josepala650/robofutbol/modelos 3d para imprimir/robot_futbool_02_rueda_loca_canica_mini.stl

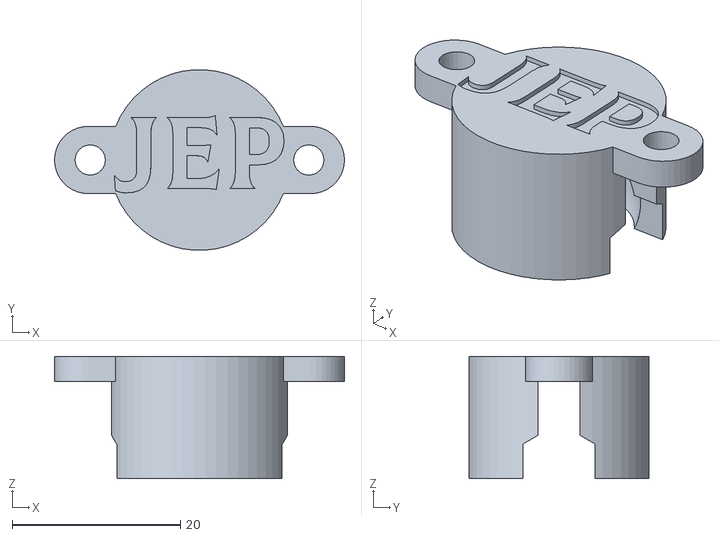
[picture p79: CAD file, 2022-09-19]
modelos 3d para imprimir/robot_futbool_02_rueda_loca_canica_mini.stl
34.5 x 21.5 x 14.6
