josepala650/robofutbol/modelos 3d para imprimir/robot_futbool_02_llanta_motor_arduino.stl

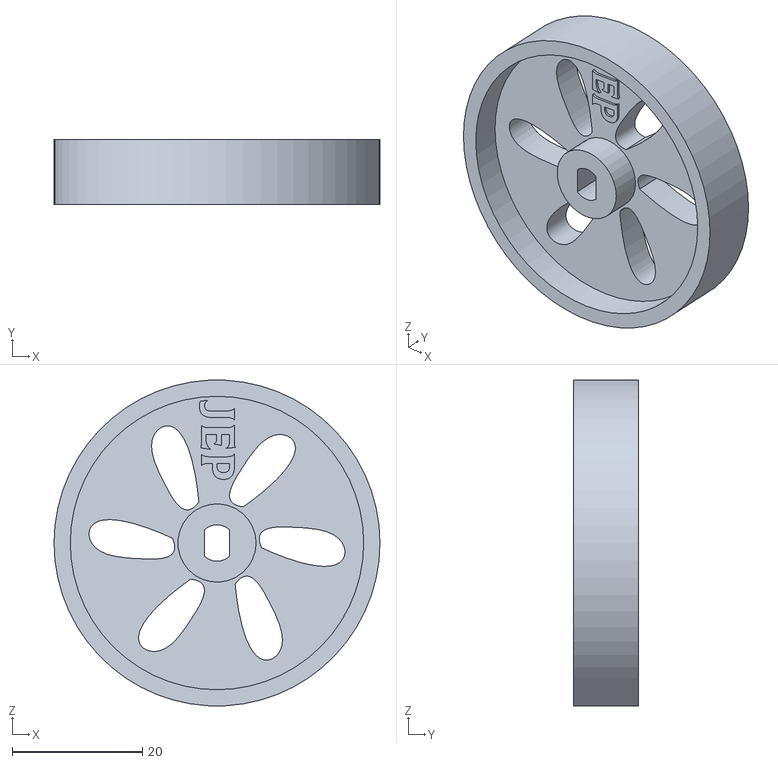
[picture p80: CAD file, 2022-09-19]
modelos 3d para imprimir/robot_futbool_02_llanta_motor_arduino.stl
50.0 x 10.0 x 49.9
