josepala650/robofutbol/modelos 3d para imprimir/robot_futbool_02_soporte ultrasonico.stl

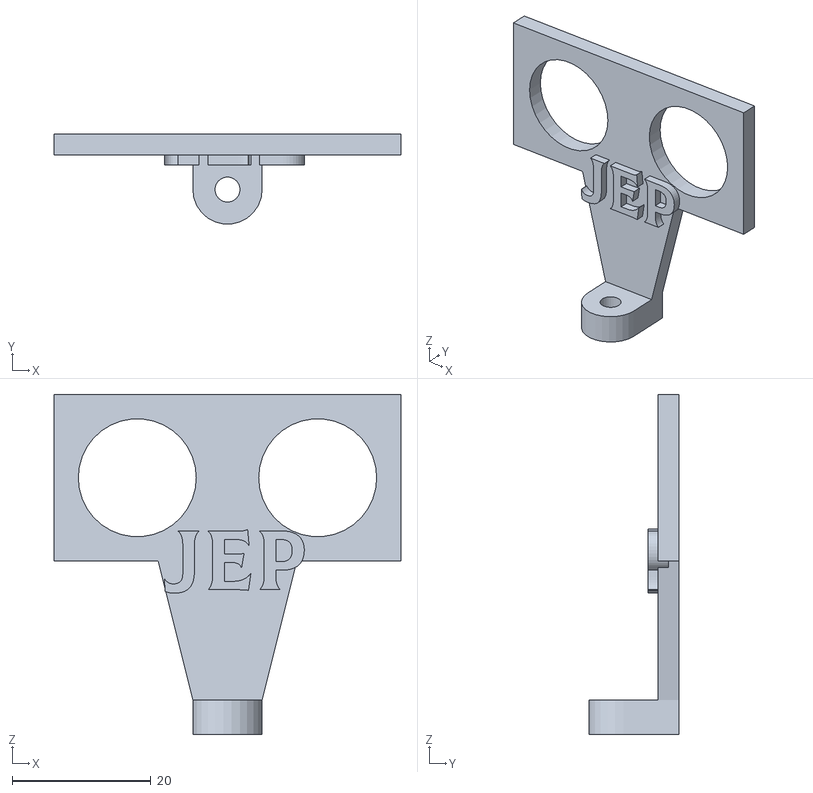
[picture p81: CAD file, 2022-09-19]
modelos 3d para imprimir/robot_futbool_02_soporte ultrasonico.stl
50.0 x 13.0 x 49.0
